JordanAceto/whooshy_sound/firmware/BSP/ADC.c

/*
--|----------------------------------------------------------------------------|
--| FILE DESCRIPTION:
--|   ADC.c provides the implementation for initializing the ADC.
--|   
--|
--|----------------------------------------------------------------------------|
--| REFERENCES:
--|   STM32L0x1 Reference Manual, page 167 (RCC)
--|   STM32L0x1 Reference Manual, page 278 (ADC)
--|
--|----------------------------------------------------------------------------|
*/

/*
--|----------------------------------------------------------------------------|
--| INCLUDE FILES
--|----------------------------------------------------------------------------|
*/

#include "stm32l031xx.h"

/*
--|----------------------------------------------------------------------------|
--| PUBLIC FUNCTION DEFINITIONS
--|----------------------------------------------------------------------------|
*/

void ADC_Init(void)
{

}
